kbob/LED-Cube/Power Board/v0.5/Power Board Models/JST_PUD_S10B-PUDSS-1_2x05x2.00mm_Angled.STEP

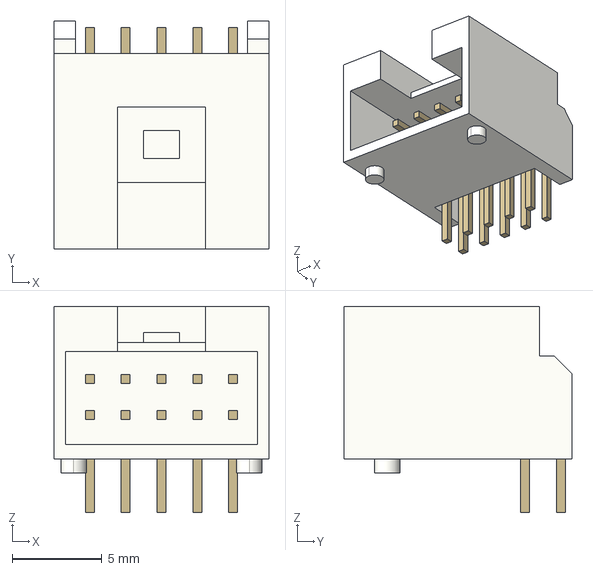
[picture p24: CAD file, 2019-04-28]
Power Board/v0.5/Power Board Models/JST_PUD_S10B-PUDSS-1_2x05x2.00mm_Angled.STEP
12.0 x 12.7 x 11.5 mm
