kbob/LED-Cube/Mechanical/Cube/Upper Link v35.stl

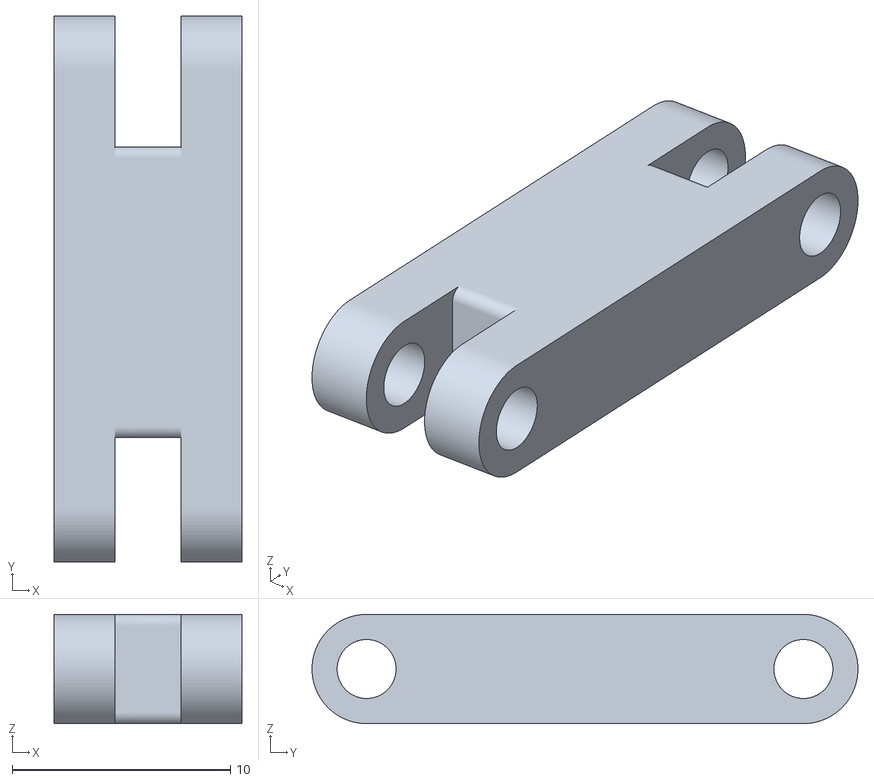
[picture p25: CAD file, 2019-09-01]
Mechanical/Cube/Upper Link v35.stl
8.60 x 25.0 x 5.00
