kbob/LED-Cube/Power Board/v0.5/Power Board Models/JST-B3PS-VH.step

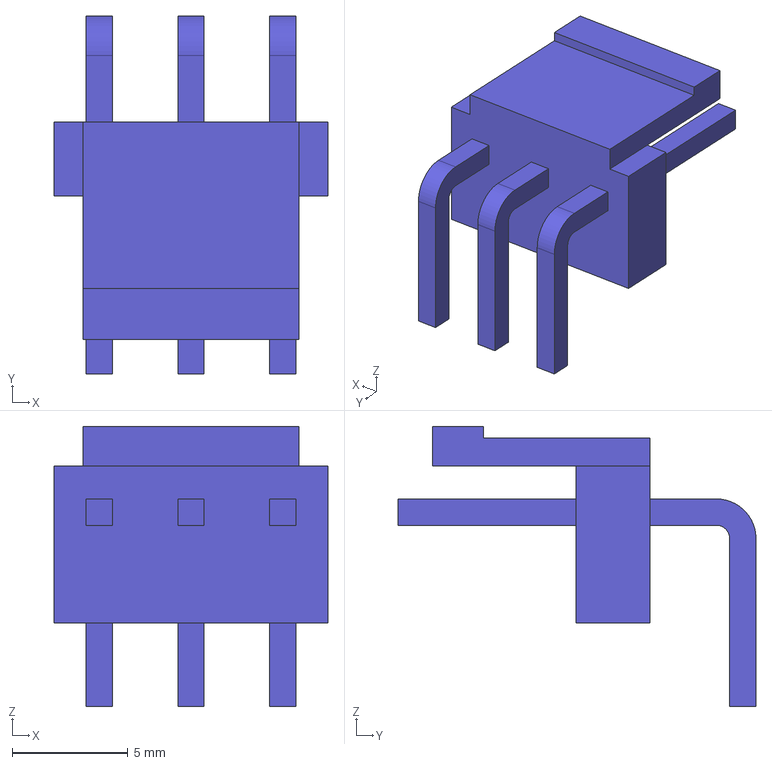
[picture p26: CAD file, 2019-04-28]
Power Board/v0.5/Power Board Models/JST-B3PS-VH.step
11.8 x 15.5 x 12.1 mm
