kbob/LED-Cube/Mechanical/Cube/Battery Carrier v64.stl

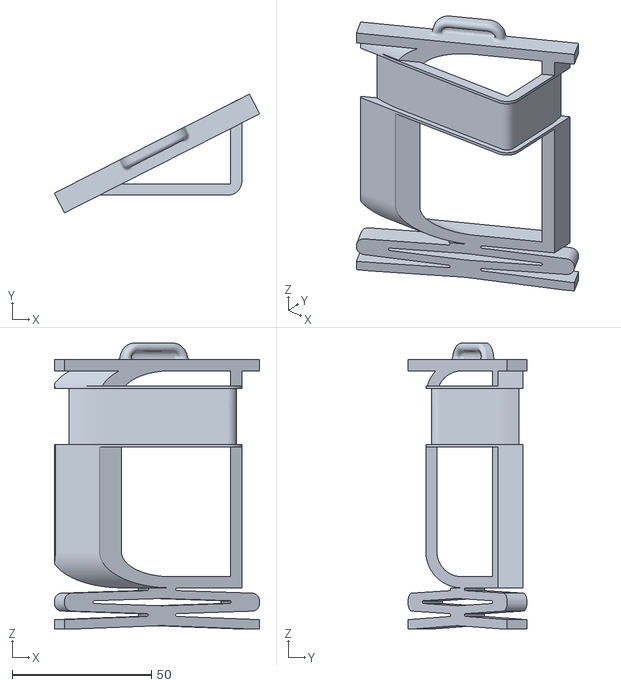
[picture p27: CAD file, 2019-09-01]
Mechanical/Cube/Battery Carrier v64.stl
73.8 x 42.7 x 102.8
