kbob/LED-Cube/Power Board/v0.5/Power Board Models/Coilcraft-XAL1580-102.step

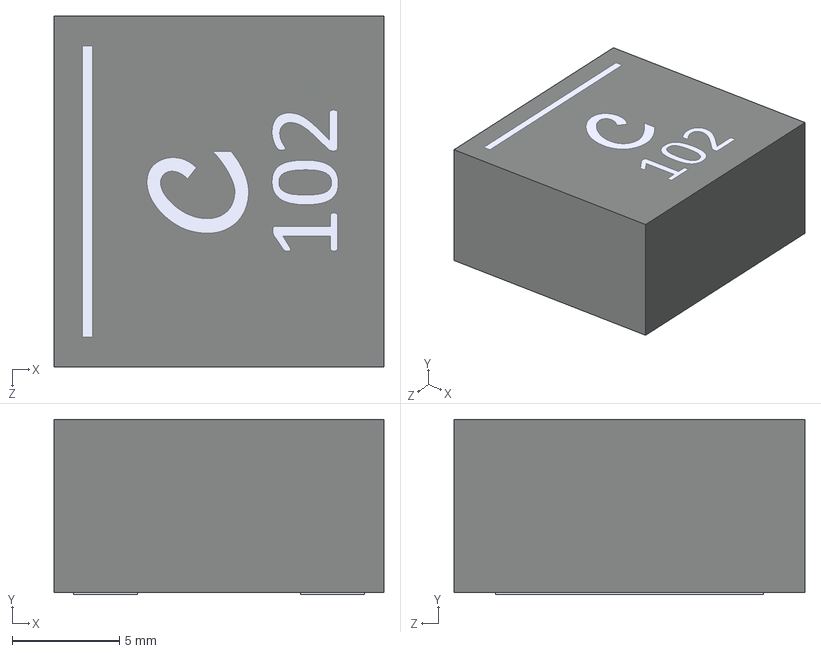
[picture p28: CAD file, 2019-04-28]
Power Board/v0.5/Power Board Models/Coilcraft-XAL1580-102.step
15.4 x 8.20 x 16.4 mm
