kbob/LED-Cube/Mechanical/Cube/Skeleton Top v53.stl

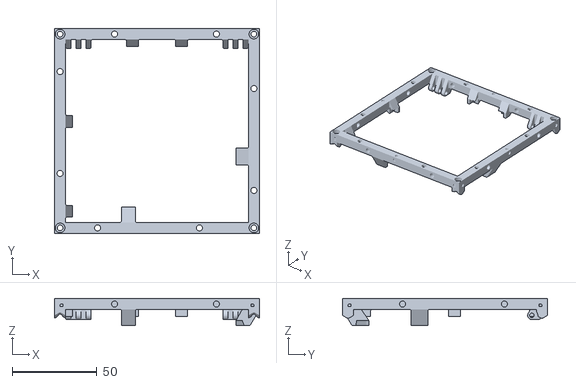
[picture p29: CAD file, 2019-09-01]
Mechanical/Cube/Skeleton Top v53.stl
120.8 x 120.8 x 16.0
