kbob/LED-Cube/Mechanical/Cube/Frame v35.stl

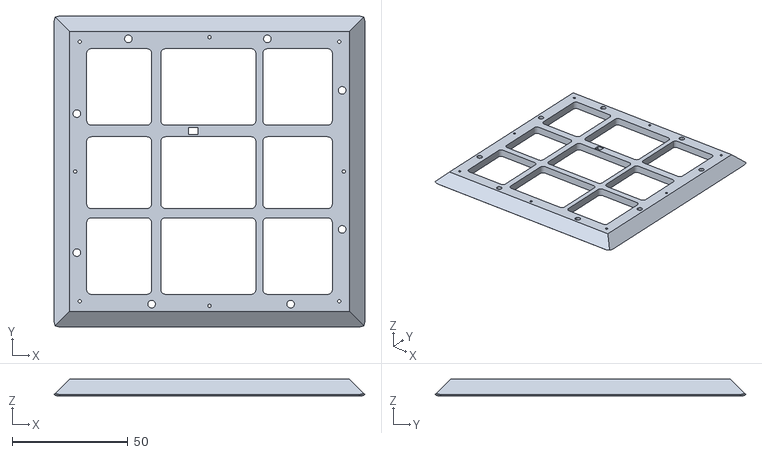
[picture p31: CAD file, 2019-09-01]
Mechanical/Cube/Frame v35.stl
134.2 x 134.2 x 7.20
