kbob/LED-Cube/Mechanical/Cube/Pi Connector Clip 4 v4.stl

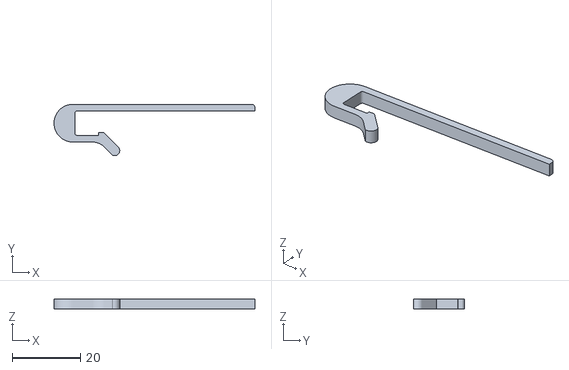
[picture p32: CAD file, 2019-09-01]
Mechanical/Cube/Pi Connector Clip 4 v4.stl
58.9 x 15.1 x 3.00
