kbob/LED-Cube/Mechanical/Cube/Left Hinge Pivot v63.stl

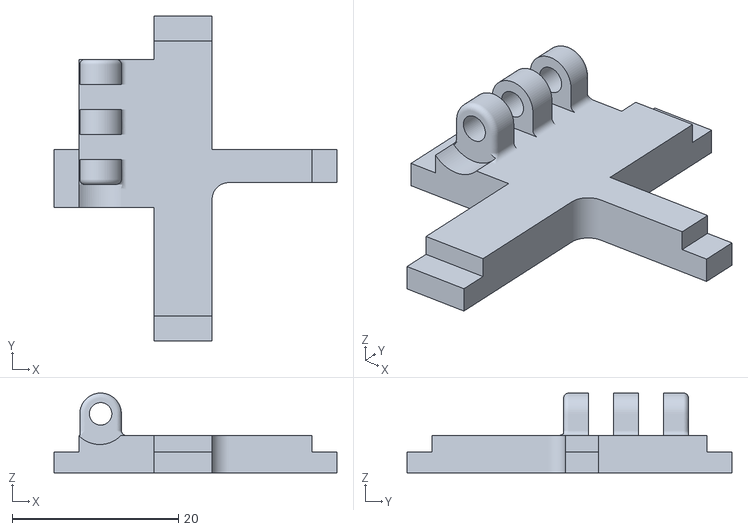
[picture p33: CAD file, 2019-09-01]
Mechanical/Cube/Left Hinge Pivot v63.stl
34.0 x 39.0 x 9.60
