kbob/LED-Cube/Mechanical/Cube/Lower Link v35.stl

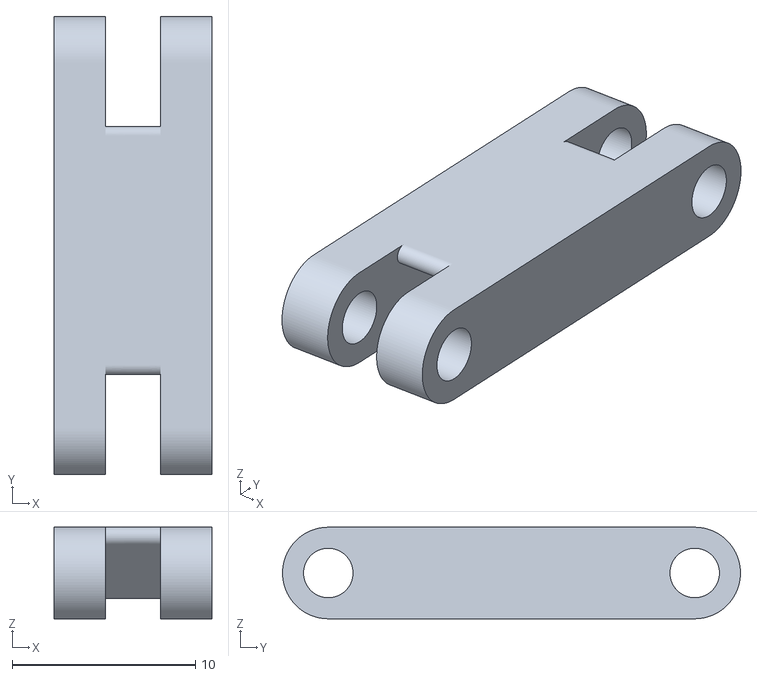
[picture p34: CAD file, 2019-09-01]
Mechanical/Cube/Lower Link v35.stl
8.60 x 25.0 x 5.00
