kbob/LED-Cube/Mechanical/Cube/Lid v35.stl

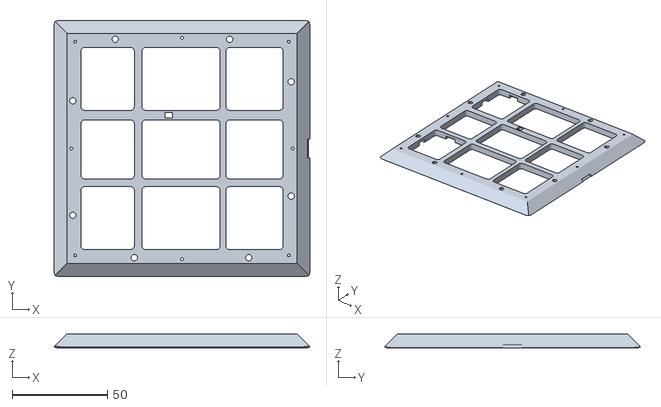
[picture p35: CAD file, 2019-09-01]
Mechanical/Cube/Lid v35.stl
134.2 x 134.2 x 7.20
