kbob/LED-Cube/Mechanical/Cube/Skeleton Bottom v59.stl

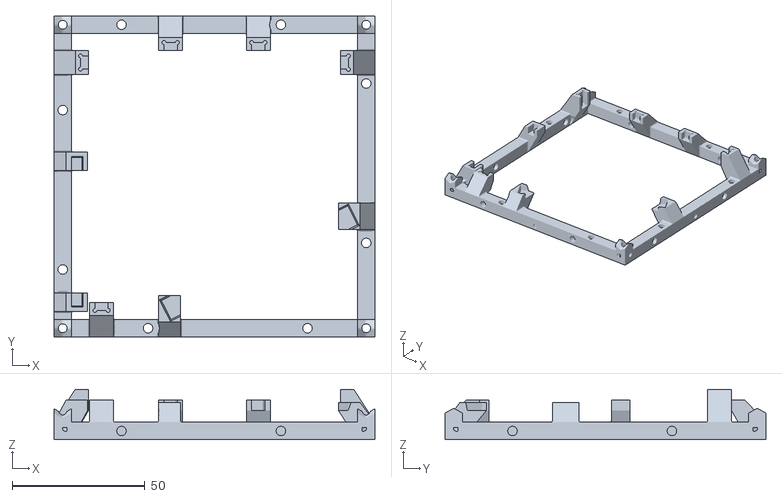
[picture p36: CAD file, 2019-09-01]
Mechanical/Cube/Skeleton Bottom v59.stl
120.8 x 120.8 x 19.0
